jonkraft/PhasedArray/GNURadio38_PhasedArrayWorkshop/ADRV9361SOM_Monopulse/ADAR1000_8_sweeper.py

# ADRV9361-SOM data collection and 2 ADAR1000 (total of 8 elements) control

'''
Useful resources:
    Introduction to Phased Array Antennas: https://www.analog.com/en/analog-dialogue/articles/phased-array-antenna-patterns-part1.html#
    Full workshop build instructions at www.github.com/jonkraft/phasedarray
    Analog Devices Python Interfaces:  https://analogdevicesinc.github.io/pyadi-iio/
    Python examples:  https://github.com/analogdevicesinc/pyadi-iio/tree/ensm-example/examples
    GNU Radio and IIO Devices:  https://wiki.analog.com/resources/tools-software/linux-software/gnuradio
    ADI Kuiper Linux for Raspberry Pi:  https://wiki.analog.com/resources/tools-software/linux-software/gnuradio
'''

# Copyright (C) 2019 Analog Devices, Inc.
#
# All rights reserved.
#
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
# IN NO EVENT SHALL ANALOG DEVICES BE LIABLE FOR ANY DIRECT, INDIRECT, INCIDENTAL, SPECIAL,
# EXEMPLARY, OR CONSEQUENTIAL DAMAGES (INCLUDING, BUT NOT LIMITED TO, INTELLECTUAL PROPERTY
# RIGHTS, PROCUREMENT OF SUBSTITUTE GOODS OR SERVICES; LOSS OF USE, DATA, OR PROFITS; OR
# BUSINESS INTERRUPTION) HOWEVER CAUSED AND ON ANY THEORY OF LIABILITY, WHETHER IN CONTRACT,
# STRICT LIABILITY, OR TORT (INCLUDING NEGLIGENCE OR OTHERWISE) ARISING IN ANY WAY OUT OF
# THE USE OF THIS SOFTWARE, EVEN IF ADVISED OF THE POSSIBILITY OF SUCH DAMAGE.


import numpy as np
import time
import spidev
from gnuradio import gr
import sys
import ipaddress

sys.path.append('/usr/lib/python2.7/site-packages/')
sys.path.append('/lib/python3.7/site-packages/')
#import iio          # see temporary issue here https://ez.analog.com/sw-interface-tools/f/q-a/534115/pyadi-iio-operation-in-gnuradio-3-8
import iiopy as iio  # this is a temporary workaround due to a conflict between gr-iio and pyadi-iio
import adi

def ADAR_init(spi, ADDR):
    # Initialize the ADAR1000
    spi.xfer2([ADDR, 0x00, 0x81])  # reset the device
    spi.xfer2([ADDR, 0x00, 0x18])  # Sets SDO  pin to active (4 wire SPI)
    spi.xfer2([ADDR+0x04, 0x00, 0x55])  # Trims LDO to 1.8V
    spi.xfer2([ADDR, 0x38, 0x60])  # Bypasses beam and bias RAM (use SPI for gain/phase)
    spi.xfer2([ADDR, 0x2E, 0x7F])  # Enables all 4 Rx channels, LNA, VGA, and Vector Mod
    spi.xfer2([ADDR, 0x34, 0x08])  # Sets LNA bias to middle of its range
    spi.xfer2([ADDR, 0x35, 0x16])  # Sets VGA bias to [0010] and vector mod bias to [110]
    spi.xfer2([ADDR, 0x31, 0xB0])  # Enables the whole Rx and sets the ADTR1107 switch high (Rx mode)
    spi.xfer2([ADDR, 0x10, int(128+127)])  # Sets Rx1 VGA gain
    spi.xfer2([ADDR, 0x11, int(128+127)])  # Sets Rx2 VGA gain
    spi.xfer2([ADDR, 0x12, int(128+127)])  # Sets Rx3 VGA gain
    spi.xfer2([ADDR, 0x13, int(128+127)])  # Sets Rx4 VGA gain

def ADAR_set_RxTaper(spi, ADDR, RxGain1, RxGain2, RxGain3, RxGain4):
    # set the ADAR1000's VGA gain of each of the Rx channels.  RxGainx needs to be between 0 and 127
    spi.xfer2([ADDR, 0x10, int(128+RxGain1)])  # Sets Rx1 VGA gain
    spi.xfer2([ADDR, 0x11, int(128+RxGain2)])  # Sets Rx2 VGA gain
    spi.xfer2([ADDR, 0x12, int(128+RxGain3)])  # Sets Rx3 VGA gain
    spi.xfer2([ADDR, 0x13, int(128+RxGain4)])  # Sets Rx4 VGA gain

def ADAR_set_RxPhase(spi, address, num_ADARs, PhDelta, phase_step_size, RxPhase1, RxPhase2, RxPhase3, RxPhase4):
    step_size = phase_step_size  #Must be 2.8125, or some multiple of that
    Phase_A = ((np.rint(PhDelta*0/step_size)*step_size) + RxPhase1) % 360  # round each value to the nearest step size increment
    Phase_B = ((np.rint(PhDelta*1/step_size)*step_size) + RxPhase2) % 360
    Phase_C = ((np.rint(PhDelta*2/step_size)*step_size) + RxPhase3) % 360
    Phase_D = ((np.rint(PhDelta*3/step_size)*step_size) + RxPhase4) % 360
    if num_ADARs == 2:
        Phase_A = ((np.rint(PhDelta*4/step_size)*step_size) + RxPhase1) % 360
        Phase_B = ((np.rint(PhDelta*5/step_size)*step_size) + RxPhase2) % 360
        Phase_C = ((np.rint(PhDelta*6/step_size)*step_size) + RxPhase3) % 360
        Phase_D = ((np.rint(PhDelta*7/step_size)*step_size) + RxPhase4) % 360
    channels = [Phase_A, Phase_B, Phase_C, Phase_D]

    # Write vector I and Q to set phase shift (see Table 13 in ADAR1000 datasheet)
    i=1
    for Channel_Phase in channels:
        #round_Phase = np.rint(Channel_Phase/step_size)*step_size
        if i==1:
            I = 0x14   # Rx1_I vector register address = 0x14
            Q = 0x15   # Rx1_Q vector register address = 0x15
        if i==2:
            I = 0x16   # Rx2_I vector register address = 0x16
            Q = 0x17   # Rx2_Q vector register address = 0x17
        if i==3:
            I = 0x18   # Rx3_I vector register address = 0x18
            Q = 0x19   # Rx3_Q vector register address = 0x19
        if i==4:
            I = 0x1A   # Rx4_I vector register address = 0x1A
            Q = 0x1B   # Rx4_Q vector register address = 0x1B
        ADAR_write_RxPhase(spi, address, Channel_Phase, I, Q)
        i = i+1
    spi.xfer2([address, 0x28, 0x01])  # Loads Rx vectors from SPI.  address of 0x08 is all ADAR1000 devices

def ADAR_write_RxPhase(spi, ADDR, Channel_Phase, I, Q):
    # See Table 13 in the ADAR1000 datasheet
    # Quadrant 1
    if Channel_Phase==0:
        spi.xfer2([ADDR, I, 0x3F])
        spi.xfer2([ADDR, Q, 0x20])
    if Channel_Phase==2.8125:
        spi.xfer2([ADDR, I, 0x3F])
        spi.xfer2([ADDR, Q, 0x21])
    if Channel_Phase==5.625:
        spi.xfer2([ADDR, I, 0x3F])
        spi.xfer2([ADDR, Q, 0x23])
    if Channel_Phase==8.4375:
        spi.xfer2([ADDR, I, 0x3F])
        spi.xfer2([ADDR, Q, 0x24])
    if Channel_Phase==11.25:
        spi.xfer2([ADDR, I, 0x3F])
        spi.xfer2([ADDR, Q, 0x26])
    if Channel_Phase==14.0625:
        spi.xfer2([ADDR, I, 0x3E])
        spi.xfer2([ADDR, Q, 0x27])
    if Channel_Phase==16.875:
        spi.xfer2([ADDR, I, 0x3E])
        spi.xfer2([ADDR, Q, 0x28])
    if Channel_Phase==19.6875:
        spi.xfer2([ADDR, I, 0x3D])
        spi.xfer2([ADDR, Q, 0x2A])
    if Channel_Phase==22.5:
        spi.xfer2([ADDR, I, 0x3D])
        spi.xfer2([ADDR, Q, 0x2B])
    if Channel_Phase==25.3125:
        spi.xfer2([ADDR, I, 0x3C])
        spi.xfer2([ADDR, Q, 0x2D])
    if Channel_Phase==28.125:
        spi.xfer2([ADDR, I, 0x3C])
        spi.xfer2([ADDR, Q, 0x2E])
    if Channel_Phase==30.9375:
        spi.xfer2([ADDR, I, 0x3B])
        spi.xfer2([ADDR, Q, 0x2F])
    if Channel_Phase==33.75:
        spi.xfer2([ADDR, I, 0x3A])
        spi.xfer2([ADDR, Q, 0x30])
    if Channel_Phase==36.5625:
        spi.xfer2([ADDR, I, 0x39])
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
    if Channel_Phase==320.625:
        spi.xfer2([ADDR, I, 0x38])
        spi.xfer2([ADDR, Q, 0x13])
    if Channel_Phase==323.4375:
        spi.xfer2([ADDR, I, 0x39])
        spi.xfer2([ADDR, Q, 0x11])
    if Channel_Phase==326.25:
        spi.xfer2([ADDR, I, 0x39])
        spi.xfer2([ADDR, Q, 0x10])
    if Channel_Phase==329.0625:
        spi.xfer2([ADDR, I, 0x3A])
        spi.xfer2([ADDR, Q, 0x0F])
    if Channel_Phase==331.875:
        spi.xfer2([ADDR, I, 0x3B])
        spi.xfer2([ADDR, Q, 0x0E])
    if Channel_Phase==334.6875:
        spi.xfer2([ADDR, I, 0x3C])
        spi.xfer2([ADDR, Q, 0x0D])
    if Channel_Phase==337.5:
        spi.xfer2([ADDR, I, 0x3C])
        spi.xfer2([ADDR, Q, 0x0B])
    if Channel_Phase==340.3125:
        spi.xfer2([ADDR, I, 0x3D])
        spi.xfer2([ADDR, Q, 0x0A])
    if Channel_Phase==343.125:
        spi.xfer2([ADDR, I, 0x3E])
        spi.xfer2([ADDR, Q, 0x08])
    if Channel_Phase==345.9375:
        spi.xfer2([ADDR, I, 0x3E])
        spi.xfer2([ADDR, Q, 0x07])
    if Channel_Phase==348.75:
        spi.xfer2([ADDR, I, 0x3E])
        spi.xfer2([ADDR, Q, 0x06])
    if Channel_Phase==351.5625:
        spi.xfer2([ADDR, I, 0x3F])
        spi.xfer2([ADDR, Q, 0x04])
    if Channel_Phase==354.375:
        spi.xfer2([ADDR, I, 0x3F])
        spi.xfer2([ADDR, Q, 0x03])
    if Channel_Phase==357.1875:
        spi.xfer2([ADDR, I, 0x3F])
        spi.xfer2([ADDR, Q, 0x01])
    

class blk(gr.sync_block):  # other base classes are basic_block, decim_block, interp_block

    def __init__(self, IP=[192, 168, 0, 3], LO_freq=2400000000, TX_freq=5810000000, SampleRate=3000000, Rx_gain=30, Averages=1, Taper=1, SymTaper=0, PhaseCal=0, SignalFreq=10525000000, RxGain1=127, RxGain2=127, RxGain3=127, RxGain4=127, RxGain5=127, RxGain6=127, RxGain7=127, RxGain8=127, Rx1_cal=0, Rx2_cal=0, Rx3_cal=0, Rx4_cal=0, Rx5_cal=0, Rx6_cal=0, Rx7_cal=0, Rx8_cal=0):  
        """arguments to this function show up as parameters in GRC"""
        gr.sync_block.__init__(
            self,
            name='ADAR1000 Sweeper',   # will show up in GRC
            in_sig=[],
            out_sig=[np.complex64, np.complex64, np.complex64, np.complex64, np.float32]
        )
        # if an attribute with the same name as a parameter is found,
        # a callback is registered (properties work, too).
        
        sdr_address = "ip:"+str(IP[0])+"."+str(IP[1])+"."+str(IP[2])+"."+str(IP[3])  # I couldn't get GNUradio to import the IP address from the flowgraph block as a string.... Not sure why.  So I broke it up into integers

        self.LO_freq = LO_freq              # RX LO freq
        self.TX_freq = TX_freq              # TX LO freq
        self.SampleRate = SampleRate
        self.Rx_gain = Rx_gain
        self.Averages = Averages
        self.Taper = Taper
        self.SymTaper = SymTaper
        self.PhaseCal = PhaseCal
        
        self.RxGain1 = RxGain1
        self.RxGain2 = RxGain2
        self.RxGain3 = RxGain3
        self.RxGain4 = RxGain4
        self.RxGain5 = RxGain5
        self.RxGain6 = RxGain6
        self.RxGain7 = RxGain7
        self.RxGain8 = RxGain8
        self.Rx1_cal=Rx1_cal
        self.Rx2_cal=Rx2_cal
        self.Rx3_cal=Rx3_cal
        self.Rx4_cal=Rx4_cal
        self.Rx5_cal=Rx5_cal
        self.Rx6_cal=Rx6_cal
        self.Rx7_cal=Rx7_cal
        self.Rx8_cal=Rx8_cal
        
        self.spi = spidev.SpiDev()
        self.spi.open(0, 0)  #set bus=0 and device=0
        self.spi.max_speed_hz = 500000
        self.spi.mode = 0
        
        # The ADDR is set by the address pins on the ADAR1000.  This is set by P10 on the eval board.
        self.ADDR1=0x20            # ADDR 0x20 is set by jumpering pins 4 and 6 on P10
        #self.ADDR1=0x00           # ADDR 0x00 is set by leaving all jumpers off of P10
        self.ADDR2 = 0x40
        ADAR_init(self.spi, self.ADDR1)
        ADAR_init(self.spi, self.ADDR2)
        
        self.c = 299792458    # speed of light in m/s
        self.d = 0.015        # element to element spacing of the antenna
        self.SignalFreq = SignalFreq
        
        '''Setup SDR Context and Configure Settings'''        
        #self.sdr=adi.ad9361(uri='ip:192.168.0.3')
        self.sdr = adi.ad9361(uri=sdr_address)
        self.sdr._ctrl.debug_attrs["adi,frequency-division-duplex-mode-enable"].value = "1"  # move to fdd mode.  see https://github.com/analogdevicesinc/pyadi-iio/blob/ensm-example/examples/ad9361_advanced_ensm.py
        self.sdr._ctrl.debug_attrs["adi,ensm-enable-txnrx-control-enable"].value = "0"       # Disable pin control so spi can move the states
        self.sdr._ctrl.debug_attrs["initialize"].value = "1"
        self.sdr._rxadc.set_kernel_buffers_count(1)   #Default is 4 Rx buffers are stored, but we want to change and immediately measure the result, so buffers=1
        rx = self.sdr._ctrl.find_channel('voltage0') 
        rx.attrs['quadrature_tracking_en'].value = '0'   # set to '1' to enable quadrature tracking
        #print(rx.attrs['quadrature_tracking_en'].value) # we are receiving a real (not complex) signal.  Therefore disable QEC, or that tracking loop will cause amplitude variation
        #self.sdr.rx_enabled_channels = [0]     # enable Rx1 (voltage0)
        self.sdr.rx_enabled_channels = [0, 1]   # enable Rx1 (voltage0) and Rx2 (voltage1)
        self.sdr.sample_rate = int(self.SampleRate)
        #self.sdr.filter = "/home/pi/Documents/PlutoFilters/samprate_40p0.ftr"  #pyadi-iio auto applies filters based on sample rate
        #self.sdr.rx_rf_bandwidth = int(1000000)
        #self.sdr.tx_rf_bandwidth = int(500000)
        self.sdr.gain_control_mode_chan0 = 'manual'      #We must be in manual gain control mode (otherwise we won't see the peaks and nulls!)
        self.sdr.gain_control_mode_chan1 = 'manual'      #We must be in manual gain control mode (otherwise we won't see the peaks and nulls!)
        self.sdr.rx_buffer_size = int(1024)    # We only need a few samples to get the gain.  And a small buffer will greatly speed up the sweep
        self.sdr.tx_hardwaregain_chan0 = -80   # Make sure the Tx channels are attenuated (or off) and their freq is far away from Rx
        self.sdr.tx_hardwaregain_chan1 = -80
        self.sdr.tx_lo = int(1000000000)
        print(self.sdr)

        
    def work(self, input_items, output_items):
        self.sdr.rx_lo = int(self.LO_freq)
        self.sdr.rx_hardwaregain_chan0 = int(self.Rx_gain)
        self.sdr.rx_hardwaregain_chan1 = int(self.Rx_gain)

        if self.Taper==0:
            if self.SymTaper==0:
                ADAR_set_RxTaper(self.spi, self.ADDR1, self.RxGain1, self.RxGain2, self.RxGain3, self.RxGain4)
                ADAR_set_RxTaper(self.spi, self.ADDR2, self.RxGain5, self.RxGain6, self.RxGain7, self.RxGain8)
            else:
                ADAR_set_RxTaper(self.spi, self.ADDR1, self.RxGain1, self.RxGain2, self.RxGain3, self.RxGain4)
                ADAR_set_RxTaper(self.spi, self.ADDR2, self.RxGain4, self.RxGain3, self.RxGain2, self.RxGain1)
        else:
            ADAR_set_RxTaper(self.spi, self.ADDR1, 127, 127, 127, 127)
            ADAR_set_RxTaper(self.spi, self.ADDR2, 127, 127, 127, 127)

        if self.PhaseCal == 0:
            Rx1_Phase_Cal = self.Rx1_cal
            Rx2_Phase_Cal = self.Rx2_cal
            Rx3_Phase_Cal = self.Rx3_cal
            Rx4_Phase_Cal = self.Rx4_cal
            Rx5_Phase_Cal = self.Rx5_cal
            Rx6_Phase_Cal = self.Rx6_cal
            Rx7_Phase_Cal = self.Rx7_cal
            Rx8_Phase_Cal = self.Rx8_cal
        else:
            Rx1_Phase_Cal = 0
            Rx2_Phase_Cal = 0
            Rx3_Phase_Cal = 0
            Rx4_Phase_Cal = 0
            Rx5_Phase_Cal = 0
            Rx6_Phase_Cal = 0
            Rx7_Phase_Cal = 0
            Rx8_Phase_Cal = 0

        phase_step_size = 2.8125
        PhaseValues = np.arange(-196.875, 196.875, phase_step_size)   # These are all the phase deltas (i.e. phase difference between Rx1 and Rx2, then Rx2 and Rx3, etc.) we'll sweep.     
        PhaseStepNumber=0    # this is the number of phase steps we'll take (140 in total).  At each phase step, we set the individual phases of each of the Rx channels
        gain = []
        angle = []
        max_signal = -100    # Reset max_signal.  We'll keep track of the maximum signal we get as we do this 140 loop.  
        max_angle = 0        # Reset max_angle.  This is the angle where we saw the max signal.  This is where our compass will point.

        for PhDelta in PhaseValues:
            ADAR_set_RxPhase(self.spi, self.ADDR1, 1, PhDelta, phase_step_size, Rx1_Phase_Cal, Rx2_Phase_Cal, Rx3_Phase_Cal, Rx4_Phase_Cal)
            ADAR_set_RxPhase(self.spi, self.ADDR2, 2, PhDelta, phase_step_size, Rx5_Phase_Cal, Rx6_Phase_Cal, Rx7_Phase_Cal, Rx8_Phase_Cal)
            # steering angle theta = arcsin(c*deltaphase/(2*pi*f*d)
            value1 = (self.c * np.radians(np.abs(PhDelta)))/(2*3.14159*self.SignalFreq*self.d)
            clamped_value1 = max(min(1, value1), -1)     #arcsin argument must be between 1 and -1, or numpy will throw a warning
            theta = np.degrees(np.arcsin(clamped_value1))
            if PhDelta>=0:
                SteerAngle = theta   # positive PhaseDelta covers 0deg to 90 deg
            else:
                SteerAngle = -theta   # negative phase delta covers 0 deg to -90 deg

            total_sum=0
            total_delta=0
            total_angle=0
            for count in range (0,self.Averages):       # repeat loop and average the results
                data=self.sdr.rx()          #read a buffer of data from Pluto using pyadi-iio library (adi.py)
                chan1 = data[0]   # Rx1 data
                chan2 = data[1]   # Rx2 data
                sum_chan = chan1+chan2
                delta_chan = chan1-chan2
                N = len(sum_chan)               #number of samples
                win = np.hamming(N)
                y_sum = sum_chan * win
                y_delta = delta_chan * win
                s_sum = np.fft.fftshift(y_sum)
                s_delta = np.fft.fftshift(y_delta)
                max_index = np.argmax(s_sum)
                total_angle = total_angle + (np.angle(s_sum[max_index]) - np.angle(s_delta[max_index]))
               
                s_mag_sum = np.abs(s_sum[max_index]) #* 2 / np.sum(win)
                s_mag_delta = np.abs(s_delta[max_index]) #* 2 / np.sum(win)
                s_dbfs_sum = 20*np.log10(np.max([s_mag_sum, 10**(-15)])/(2**12))        # make sure the log10 argument isn't zero (hence np.max)
                s_dbfs_delta = 20*np.log10(np.max([s_mag_delta, 10**(-15)])/(2**12))    # make sure the log10 argument isn't zero (hence np.max)
                total_sum=total_sum+(s_dbfs_sum)   # sum up all the loops, then we'll average
                total_delta=total_delta+(s_dbfs_delta)   # sum up all the loops, then we'll average
            PeakValue_sum = total_sum/self.Averages
            PeakValue_delta = total_delta/self.Averages
            PeakValue_angle = total_angle/self.Averages
            
            if PeakValue_angle > 0:
                diff_angle = 1
                diff_chan = max((diff_angle * (PeakValue_sum - PeakValue_delta) + diff_angle * (PeakValue_sum + PeakValue_delta)/2) / (PeakValue_sum + PeakValue_delta), 0.01)
            else:
                diff_angle = -1
                diff_chan = min((diff_angle * (PeakValue_sum - PeakValue_delta) + diff_angle * (PeakValue_sum + PeakValue_delta)/2) / (PeakValue_sum + PeakValue_delta), -0.01)
            #diff_angle=PeakValue_angle
            #diff_chan = (diff_angle * (PeakValue_sum - PeakValue_delta) + diff_angle * (PeakValue_sum + PeakValue_delta)/2) / (PeakValue_sum + PeakValue_delta)
            #diff_chan = PeakValue_sum - PeakValue_delta

            if PeakValue_sum>max_signal:    #take the largest value, so that we know where to point the compass
                max_signal=PeakValue_sum
                max_angle=PhDelta
                
            output_items[0][PhaseStepNumber]=((1)*SteerAngle + (1j * PeakValue_sum))  # output this as a complex number so we can do an x-y plot with the constellation graph
            output_items[1][PhaseStepNumber]=((1)*SteerAngle + (1j * PeakValue_delta))  # output this as a complex number so we can do an x-y plot with the constellation graph
            output_items[2][PhaseStepNumber]=((1)*SteerAngle + (1j * diff_chan))  # output this as a complex number so we can do an x-y plot with the constellation graph
            output_items[3][PhaseStepNumber]=((1)*SteerAngle + (1j * diff_angle))  # output this as a complex number so we can do an x-y plot with the constellation graph
            PhaseStepNumber=PhaseStepNumber+1    # increment the phase delta and start this whole again.  This will repeat 140 times

        output_items[0]=output_items[0][0:PhaseStepNumber]
        output_items[1]=output_items[1][0:PhaseStepNumber]
        output_items[2]=output_items[2][0:PhaseStepNumber]
        output_items[3]=output_items[3][0:PhaseStepNumber]
        output_items[4][:] = max_angle #* (-1)+90
            
        return len(output_items[0])
