jonkraft/PhasedArray/GNURadio38_PhasedArrayWorkshop/Pluto_FFTwPhaseChange/epy_block_0.py

# ADAR1000 Phase Control and Steering Angle Calculation

'''
Useful resources:
    Introduction to Phased Array Antennas: https://www.analog.com/en/analog-dialogue/articles/phased-array-antenna-patterns-part1.html#
    Full workshop build instructions at www.github.com/jonkraft/phasedarray
    Analog Devices Python Interfaces:  https://analogdevicesinc.github.io/pyadi-iio/
    Python examples:  https://github.com/analogdevicesinc/pyadi-iio/tree/ensm-example/examples
    GNU Radio and IIO Devices:  https://wiki.analog.com/resources/tools-software/linux-software/gnuradio
    ADI Kuiper Linux for Raspberry Pi:  https://wiki.analog.com/resources/tools-software/linux-software/gnuradio
'''

# Copyright (C) 2019 Analog Devices, Inc.
#
# All rights reserved.
#
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
# IN NO EVENT SHALL ANALOG DEVICES BE LIABLE FOR ANY DIRECT, INDIRECT, INCIDENTAL, SPECIAL,
# EXEMPLARY, OR CONSEQUENTIAL DAMAGES (INCLUDING, BUT NOT LIMITED TO, INTELLECTUAL PROPERTY
# RIGHTS, PROCUREMENT OF SUBSTITUTE GOODS OR SERVICES; LOSS OF USE, DATA, OR PROFITS; OR
# BUSINESS INTERRUPTION) HOWEVER CAUSED AND ON ANY THEORY OF LIABILITY, WHETHER IN CONTRACT,
# STRICT LIABILITY, OR TORT (INCLUDING NEGLIGENCE OR OTHERWISE) ARISING IN ANY WAY OUT OF
# THE USE OF THIS SOFTWARE, EVEN IF ADVISED OF THE POSSIBILITY OF SUCH DAMAGE.


import numpy as np
import time
import spidev
from gnuradio import gr

class blk(gr.sync_block):  # other base classes are basic_block, decim_block, interp_block

    def __init__(self, PhaseDelta=45, SignalFreq=10525000000, UpdateRate=2, Rx1_Phase_Cal=0, Rx2_Phase_Cal=0, Rx3_Phase_Cal=0, Rx4_Phase_Cal=0):  # only default arguments here
        """arguments to this function show up as parameters in GRC"""
        gr.sync_block.__init__(
            self,
            name='Calculate Steering Angle',   # will show up in GRC
            in_sig=[],   # we have no flowgraph inputs to this block
            out_sig=[np.float32]   # we have one flowgraph output, which is the calculated steering angle
        )
        # if an attribute with the same name as a parameter is found,
        # a callback is registered (properties work, too).
        self.UpdateRate = UpdateRate
        self.PhaseDelta = PhaseDelta
        self.Rx1_Phase_Cal = Rx1_Phase_Cal
        self.Rx2_Phase_Cal = Rx2_Phase_Cal
        self.Rx3_Phase_Cal = Rx3_Phase_Cal
        self.Rx4_Phase_Cal = Rx4_Phase_Cal

        # The ADDR is set by the address pins on the ADAR1000.  This is set by P10 on the eval board.
        self.ADDR=0x20            # ADDR 0x20 is set by jumpering pins 4 and 6 on P10
        #self.ADDR=0x00           # ADDR 0x00 is set by leaving all jumpers off of P10
        
        self.c = 299792458    # speed of light in m/s
        self.d = 0.015        # element to element spacing of the antenna
        self.f = SignalFreq
               
        self.spi = spidev.SpiDev()
        self.spi.open(0, 0)  #set bus=0 and device=0
        self.spi.max_speed_hz = 500000
        self.spi.mode = 0

        # Initialize the ADAR1000
        self.spi.xfer2([self.ADDR, 0x00, 0x81])  # reset the device
        self.spi.xfer2([self.ADDR, 0x00, 0x18])  # Sets SDO  pin to active (4 wire SPI)
        self.spi.xfer2([self.ADDR+0x04, 0x00, 0x55])  # Trims LDO to 1.8V
        self.spi.xfer2([self.ADDR, 0x38, 0x60])  # Bypasses beam and bias RAM (use SPI for gain/phase)
        self.spi.xfer2([self.ADDR, 0x2E, 0x7F])  # Enables all 4 Rx channels, LNA, VGA, and Vector Mod
        self.spi.xfer2([self.ADDR, 0x34, 0x08])  # Sets LNA bias to middle of its range
        self.spi.xfer2([self.ADDR, 0x35, 0x16])  # Sets VGA bias to [0010] and vector mod bias to [110]
        self.spi.xfer2([self.ADDR, 0x31, 0x20])  # Enables the whole Rx

        # Write registers to set Rx1-4 to Max Gain
        self.spi.xfer2([self.ADDR, 0x10, 0xFF])  # Sets Rx1 to max gain
        self.spi.xfer2([self.ADDR, 0x11, 0xFF])  # Sets Rx2 to max gain
        self.spi.xfer2([self.ADDR, 0x12, 0xFF])  # Sets Rx3 to max gain
        self.spi.xfer2([self.ADDR, 0x13, 0xFF])  # Sets Rx4 to max gain

    def work(self, input_items, output_items):
        # steering angle theta = arcsin(c*deltaphase/(2*pi*f*d)
        # if element spacing is lambda/2 then this simplifies to theta=arcsin(deltaphase(in radians)/pi)
        value1 = (self.c * np.radians(np.abs(self.PhaseDelta)))/(2*3.14159*self.f*self.d)
        clamped_value1 = max(min(1, value1), -1)     #arcsin argument must be between 1 and -1, or numpy will throw a warning
        theta = np.degrees(np.arcsin(clamped_value1))
        if self.PhaseDelta>=0:
            SteerAngle = 90-theta   # positive PhaseDelta covers 0deg to 90 deg
        else:
            SteerAngle = 90+theta # negative phase delta covers 0 deg to -90 deg
            
        step_size = 2.8125
        Phase_A = ((np.rint(self.PhaseDelta*0/step_size)*step_size) + self.Rx1_Phase_Cal) % 360
        Phase_B = ((np.rint(self.PhaseDelta*1/step_size)*step_size) + self.Rx2_Phase_Cal) % 360
        Phase_C = ((np.rint(self.PhaseDelta*2/step_size)*step_size) + self.Rx3_Phase_Cal) % 360
        Phase_D = ((np.rint(self.PhaseDelta*3/step_size)*step_size) + self.Rx4_Phase_Cal) % 360
        channels = [Phase_A, Phase_B, Phase_C, Phase_D]

        # Write vector I and Q to set Rx1 (see Table 13 in ADAR1000 datasheet)
        i=1
        for Channel_Phase in channels:
            #Channel_Phase = self.Rx1_phase     # Which Rx phase control channel are we looking at?
            if i==1:
                I = 0x14   # Rx1_I vector register address = 0x14
                Q = 0x15   # Rx1_Q vector register address = 0x15
            if i==2:
                I = 0x16   # Rx2_I vector register address = 0x16
                Q = 0x17   # Rx2_Q vector register address = 0x17
            if i==3:
                I = 0x18   # Rx3_I vector register address = 0x18
                Q = 0x19   # Rx3_Q vector register address = 0x19
            if i==4:
                I = 0x1A   # Rx4_I vector register address = 0x1A
                Q = 0x1B   # Rx4_Q vector register address = 0x1B
            i = i+1

            # See Table 13 in the ADAR1000 datasheet
            # Quadrant 1
            if Channel_Phase==0:
                self.spi.xfer2([self.ADDR, I, 0x3F])
                self.spi.xfer2([self.ADDR, Q, 0x20])
            if Channel_Phase==2.8125:
                self.spi.xfer2([self.ADDR, I, 0x3F])
                self.spi.xfer2([self.ADDR, Q, 0x21])
            if Channel_Phase==5.625:
                self.spi.xfer2([self.ADDR, I, 0x3F])
                self.spi.xfer2([self.ADDR, Q, 0x23])
            if Channel_Phase==8.4375:
                self.spi.xfer2([self.ADDR, I, 0x3F])
                self.spi.xfer2([self.ADDR, Q, 0x24])
            if Channel_Phase==11.25:
                self.spi.xfer2([self.ADDR, I, 0x3F])
                self.spi.xfer2([self.ADDR, Q, 0x26])
            if Channel_Phase==14.0625:
                self.spi.xfer2([self.ADDR, I, 0x3E])
                self.spi.xfer2([self.ADDR, Q, 0x27])
            if Channel_Phase==16.875:
                self.spi.xfer2([self.ADDR, I, 0x3E])
                self.spi.xfer2([self.ADDR, Q, 0x28])
            if Channel_Phase==19.6875:
                self.spi.xfer2([self.ADDR, I, 0x3D])
                self.spi.xfer2([self.ADDR, Q, 0x2A])
            if Channel_Phase==22.5:
                self.spi.xfer2([self.ADDR, I, 0x3D])
                self.spi.xfer2([self.ADDR, Q, 0x2B])
            if Channel_Phase==25.3125:
                self.spi.xfer2([self.ADDR, I, 0x3C])
                self.spi.xfer2([self.ADDR, Q, 0x2D])
            if Channel_Phase==28.125:
                self.spi.xfer2([self.ADDR, I, 0x3C])
                self.spi.xfer2([self.ADDR, Q, 0x2E])
            if Channel_Phase==30.9375:
                self.spi.xfer2([self.ADDR, I, 0x3B])
                self.spi.xfer2([self.ADDR, Q, 0x2F])
            if Channel_Phase==33.75:
                self.spi.xfer2([self.ADDR, I, 0x3A])
                self.spi.xfer2([self.ADDR, Q, 0x30])
            if Channel_Phase==36.5625:
                self.spi.xfer2([self.ADDR, I, 0x39])
                self.spi.xfer2([self.ADDR, Q, 0x31])
            if Channel_Phase==39.375:
                self.spi.xfer2([self.ADDR, I, 0x38])
                self.spi.xfer2([self.ADDR, Q, 0x33])
            if Channel_Phase==42.1875:
                self.spi.xfer2([self.ADDR, I, 0x37])
                self.spi.xfer2([self.ADDR, Q, 0x34])
            if Channel_Phase==45:
                self.spi.xfer2([self.ADDR, I, 0x36])
                self.spi.xfer2([self.ADDR, Q, 0x35])
            if Channel_Phase==47.8125:
                self.spi.xfer2([self.ADDR, I, 0x35])
                self.spi.xfer2([self.ADDR, Q, 0x36])
            if Channel_Phase==50.625:
                self.spi.xfer2([self.ADDR, I, 0x34])
                self.spi.xfer2([self.ADDR, Q, 0x37])
            if Channel_Phase==53.4375:
                self.spi.xfer2([self.ADDR, I, 0x33])
                self.spi.xfer2([self.ADDR, Q, 0x38])
            if Channel_Phase==56.25:
                self.spi.xfer2([self.ADDR, I, 0x32])
                self.spi.xfer2([self.ADDR, Q, 0x38])
            if Channel_Phase==59.0625:
                self.spi.xfer2([self.ADDR, I, 0x30])
                self.spi.xfer2([self.ADDR, Q, 0x39])
            if Channel_Phase==61.875:
                self.spi.xfer2([self.ADDR, I, 0x2F])
                self.spi.xfer2([self.ADDR, Q, 0x3A])
            if Channel_Phase==64.6875:
                self.spi.xfer2([self.ADDR, I, 0x2E])
                self.spi.xfer2([self.ADDR, Q, 0x3A])
            if Channel_Phase==67.5:
                self.spi.xfer2([self.ADDR, I, 0x2C])
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
                self.spi.xfer2([self.ADDR, Q, 0x13])
            if Channel_Phase==323.4375:
                self.spi.xfer2([self.ADDR, I, 0x39])
                self.spi.xfer2([self.ADDR, Q, 0x11])
            if Channel_Phase==326.25:
                self.spi.xfer2([self.ADDR, I, 0x39])
                self.spi.xfer2([self.ADDR, Q, 0x10])
            if Channel_Phase==329.0625:
                self.spi.xfer2([self.ADDR, I, 0x3A])
                self.spi.xfer2([self.ADDR, Q, 0x0F])
            if Channel_Phase==331.875:
                self.spi.xfer2([self.ADDR, I, 0x3B])
                self.spi.xfer2([self.ADDR, Q, 0x0E])
            if Channel_Phase==334.6875:
                self.spi.xfer2([self.ADDR, I, 0x3C])
                self.spi.xfer2([self.ADDR, Q, 0x0D])
            if Channel_Phase==337.5:
                self.spi.xfer2([self.ADDR, I, 0x3C])
                self.spi.xfer2([self.ADDR, Q, 0x0B])
            if Channel_Phase==340.3125:
                self.spi.xfer2([self.ADDR, I, 0x3D])
                self.spi.xfer2([self.ADDR, Q, 0x0A])
            if Channel_Phase==343.125:
                self.spi.xfer2([self.ADDR, I, 0x3E])
                self.spi.xfer2([self.ADDR, Q, 0x08])
            if Channel_Phase==345.9375:
                self.spi.xfer2([self.ADDR, I, 0x3E])
                self.spi.xfer2([self.ADDR, Q, 0x07])
            if Channel_Phase==348.75:
                self.spi.xfer2([self.ADDR, I, 0x3E])
                self.spi.xfer2([self.ADDR, Q, 0x06])
            if Channel_Phase==351.5625:
                self.spi.xfer2([self.ADDR, I, 0x3F])
                self.spi.xfer2([self.ADDR, Q, 0x04])
            if Channel_Phase==354.375:
                self.spi.xfer2([self.ADDR, I, 0x3F])
                self.spi.xfer2([self.ADDR, Q, 0x03])
            if Channel_Phase==357.1875:
                self.spi.xfer2([self.ADDR, I, 0x3F])
                self.spi.xfer2([self.ADDR, Q, 0x01])
                
        self.spi.xfer2([self.ADDR, 0x28, 0x01])  # Loads Rx vectors from SPI.
        time.sleep(self.UpdateRate)
        output_items[0][:] = SteerAngle * (-1) + 90
        
        return len(output_items[0])
